IBRAM2/Scoreboard_TableTennis/Kicad/PCBs/2023-06-08_12-18-55.png

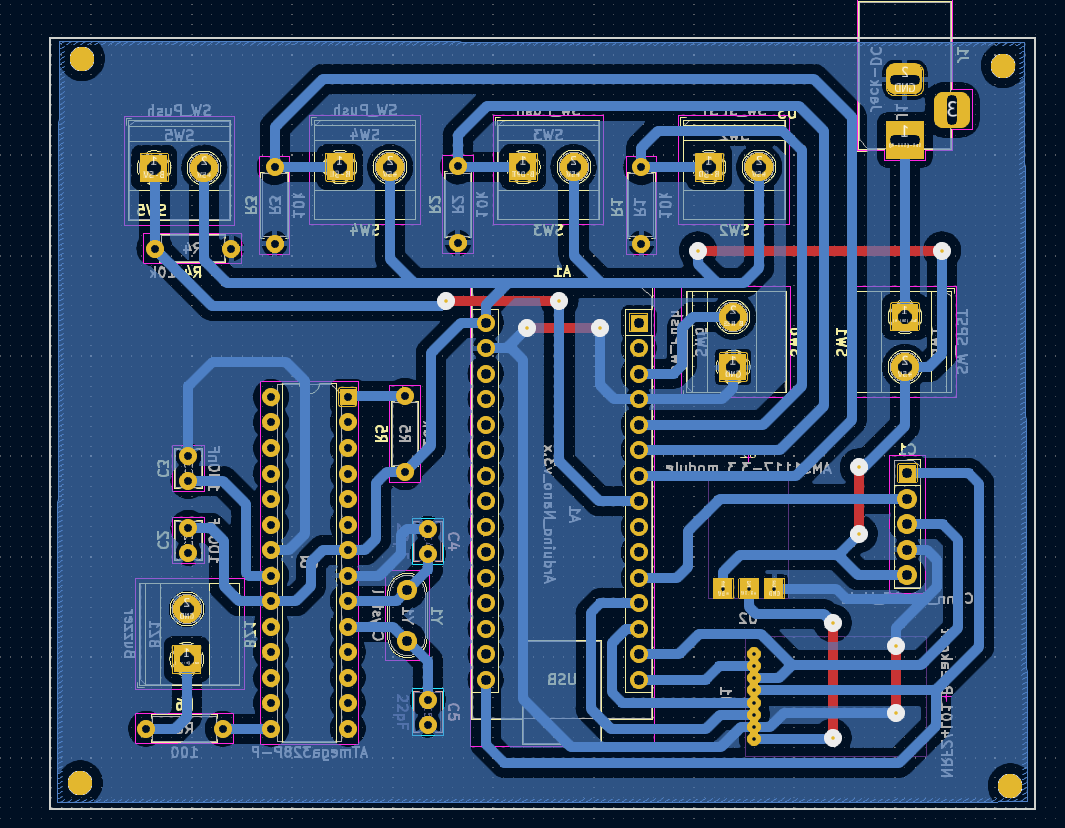
Kicad/PCBs/2023-06-08_12-18-55.png
