IBRAM2/Scoreboard_TableTennis/Kicad/PCBs/2023-06-08_13-09-04.png

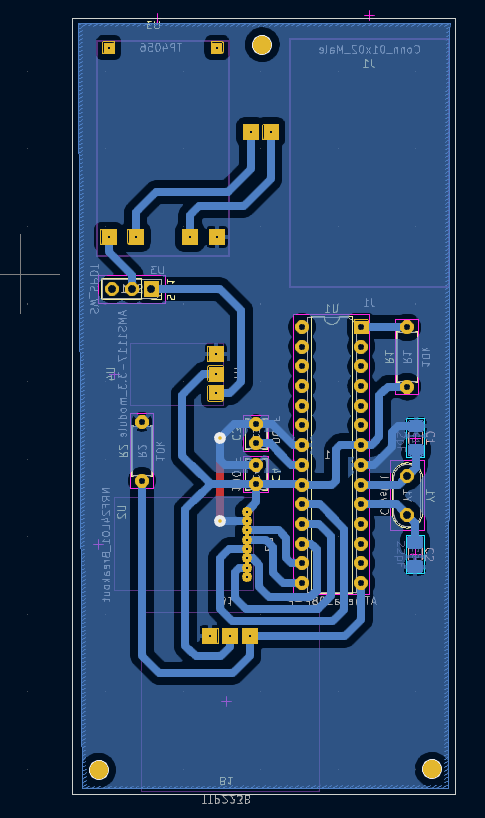
Kicad/PCBs/2023-06-08_13-09-04.png
